sdz-mods/SGI_O2_PROM_ISP/9.PHOTOS/S3.jpg

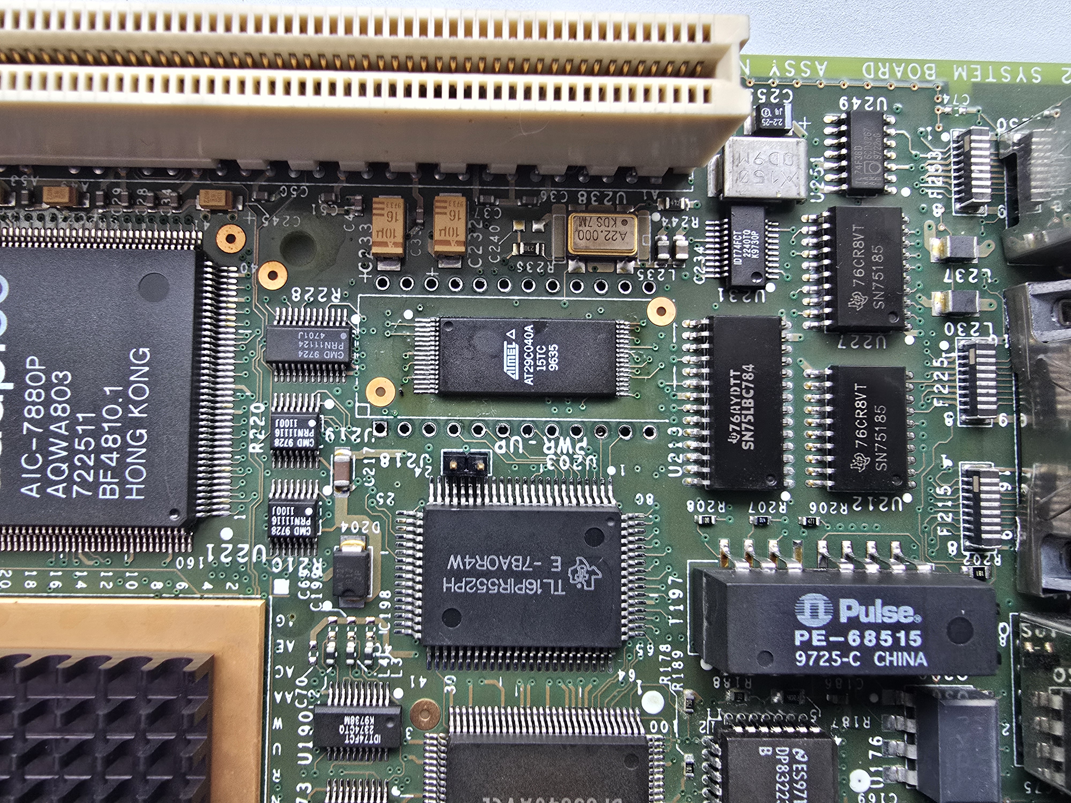
9.PHOTOS/S3.jpg
