sdz-mods/SGI_O2_PROM_ISP/9.PHOTOS/S7.jpg

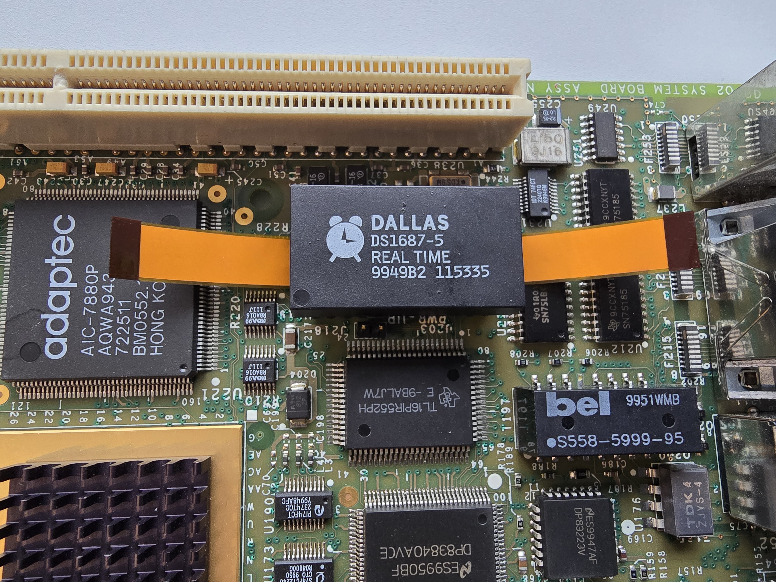
9.PHOTOS/S7.jpg
